Ranpo98/Safe_Crib_with_Auto_Detection/CAD/1.JPG

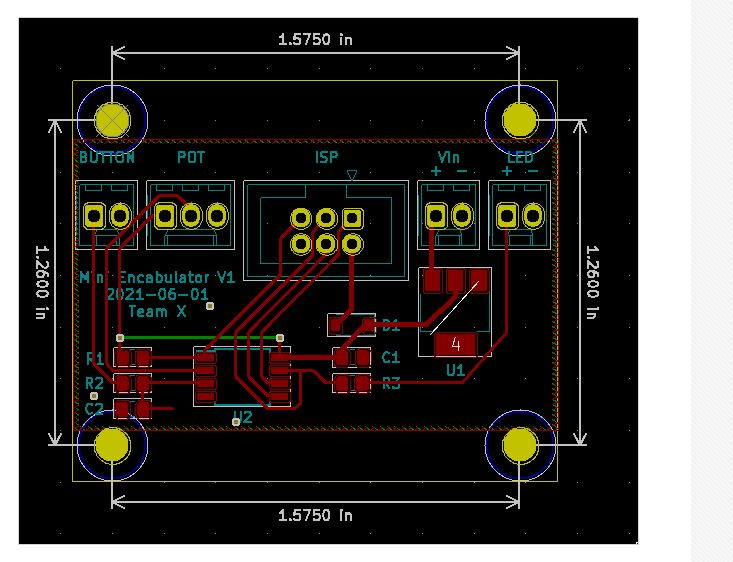
CAD/1.JPG
