Ranpo98/Safe_Crib_with_Auto_Detection/CAD/2.JPG

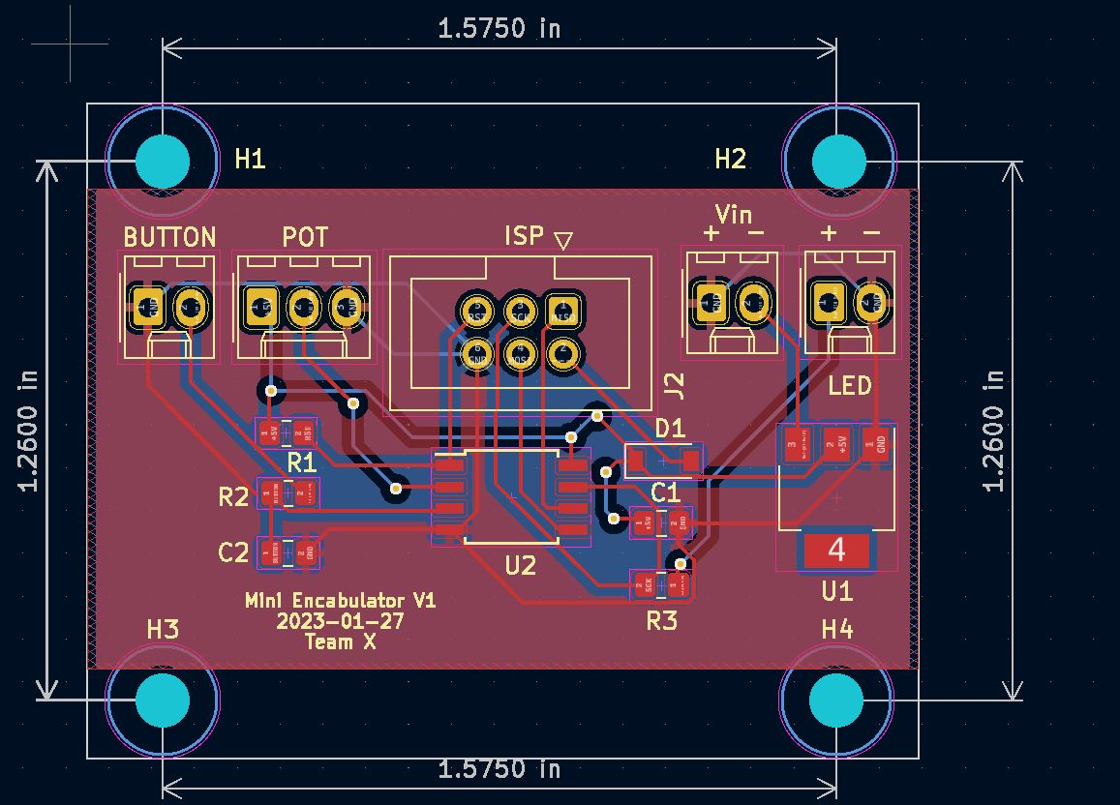
CAD/2.JPG
