Ranpo98/Safe_Crib_with_Auto_Detection/CAD/[fengz3]_miniencabulator/4.JPG

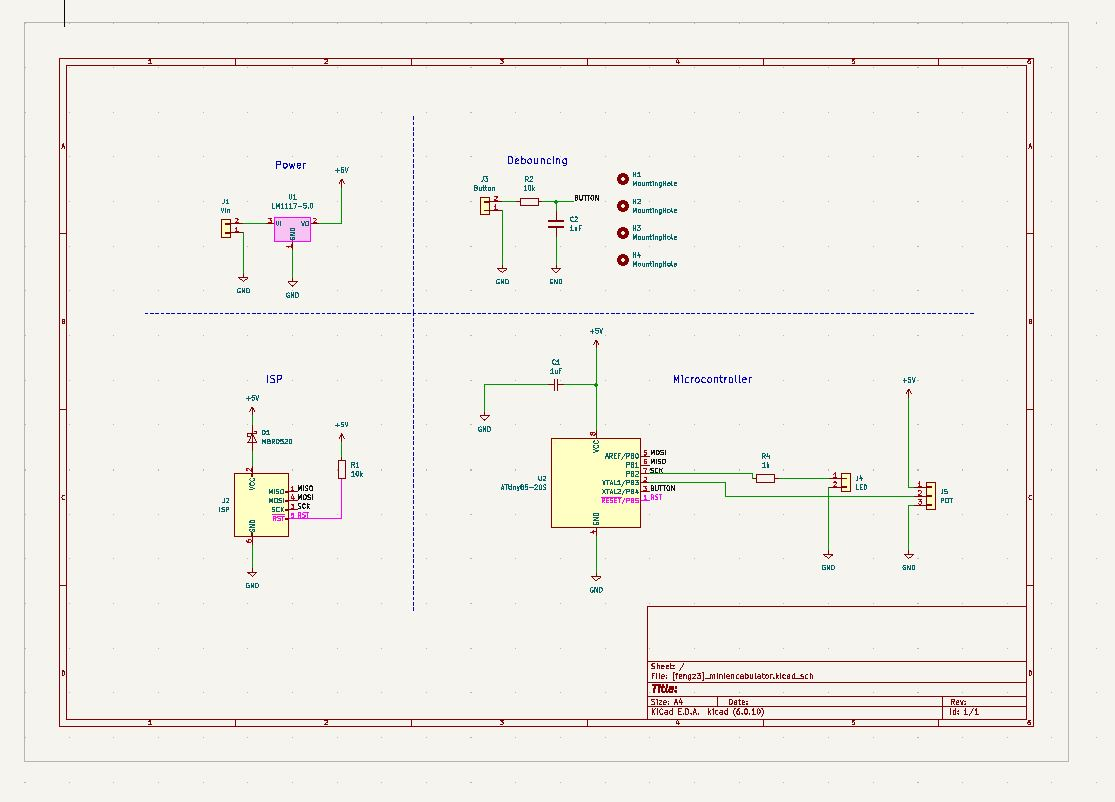
CAD/[fengz3]_miniencabulator/4.JPG
