Ranpo98/Safe_Crib_with_Auto_Detection/Feng's Notebooks/crib model.png

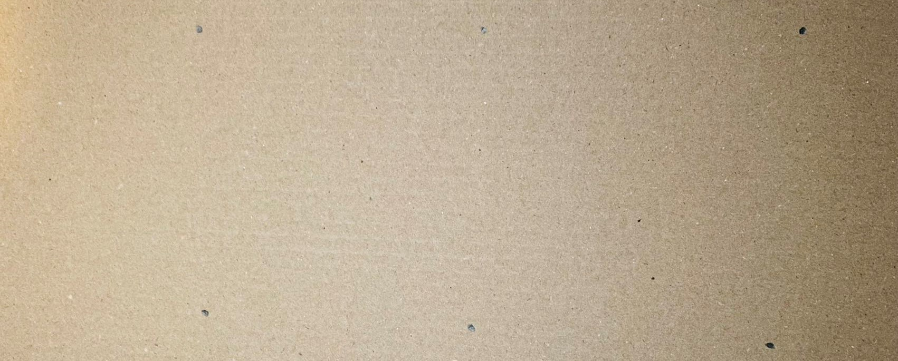
Feng's Notebooks/crib model.png
