Ranpo98/Safe_Crib_with_Auto_Detection/Feng's Notebooks/crosstalk 2.PNG

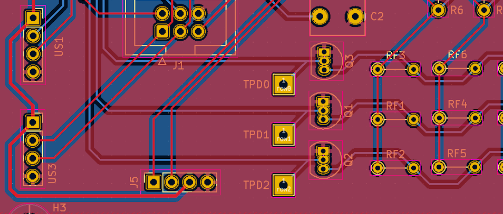
Feng's Notebooks/crosstalk 2.PNG
