Ranpo98/Safe_Crib_with_Auto_Detection/Feng's Notebooks/N3.jpg

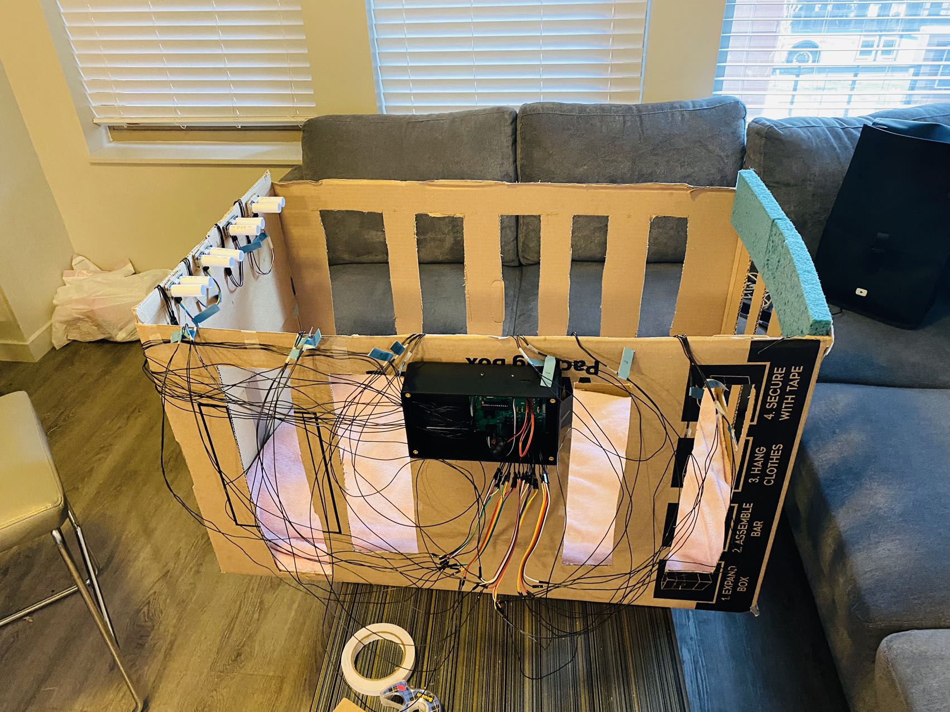
Feng's Notebooks/N3.jpg
