Ranpo98/Safe_Crib_with_Auto_Detection/Feng's Notebooks/N4.jpg

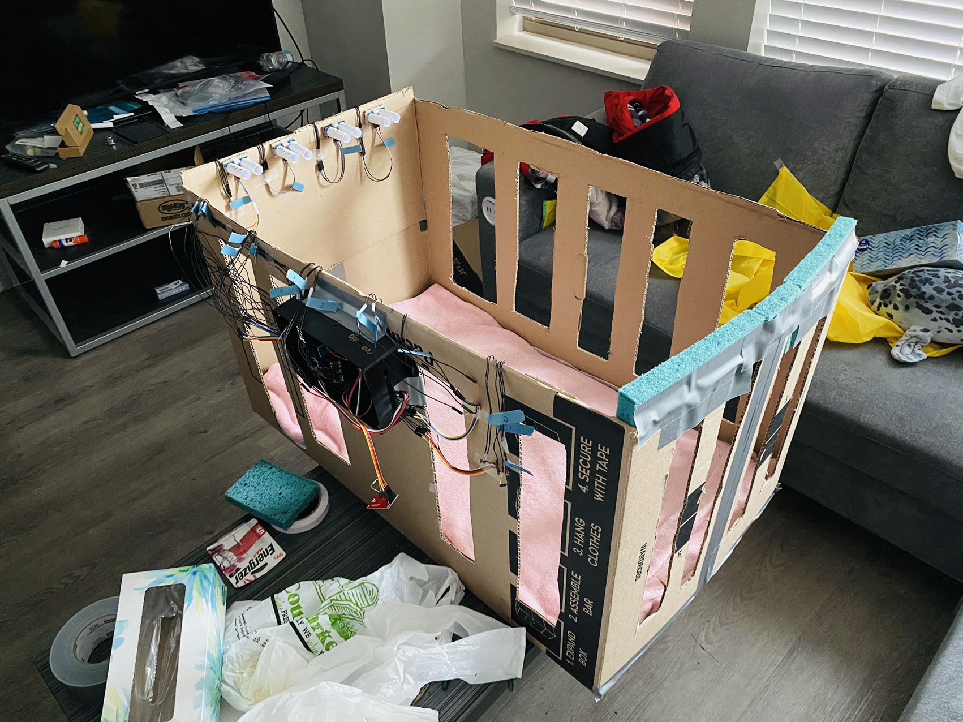
Feng's Notebooks/N4.jpg
