Ranpo98/Safe_Crib_with_Auto_Detection/Feng's Notebooks/Table_Sound.PNG

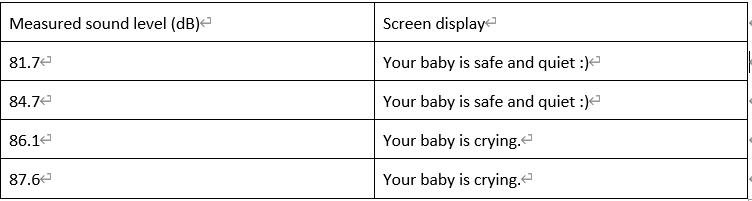
Feng's Notebooks/Table_Sound.PNG
