Ranpo98/Safe_Crib_with_Auto_Detection/Images/image7.png

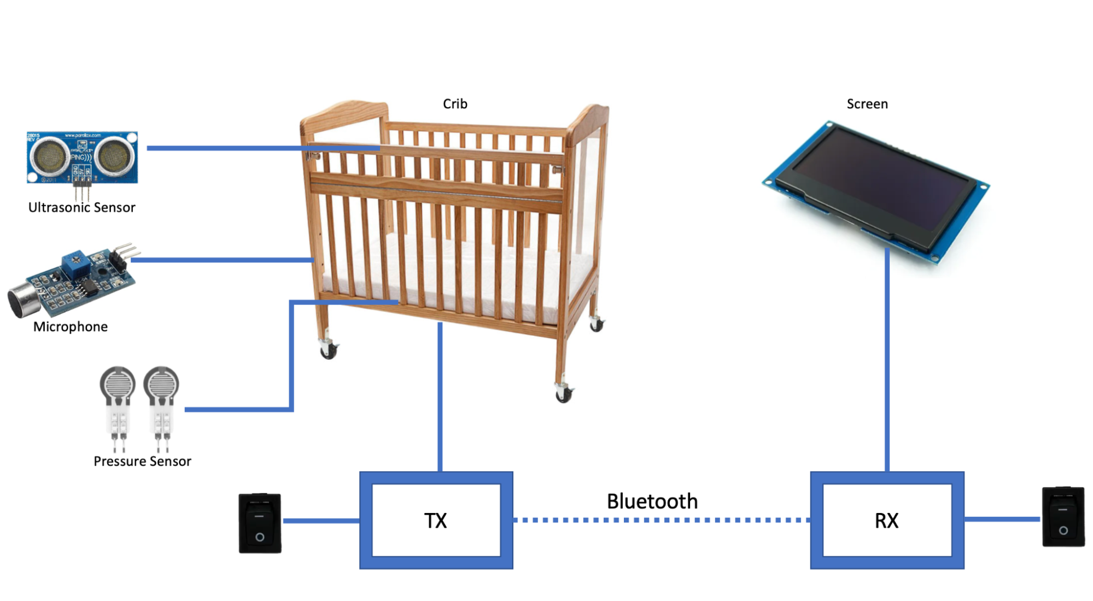
Images/image7.png
