Ranpo98/Safe_Crib_with_Auto_Detection/Images/image8.png

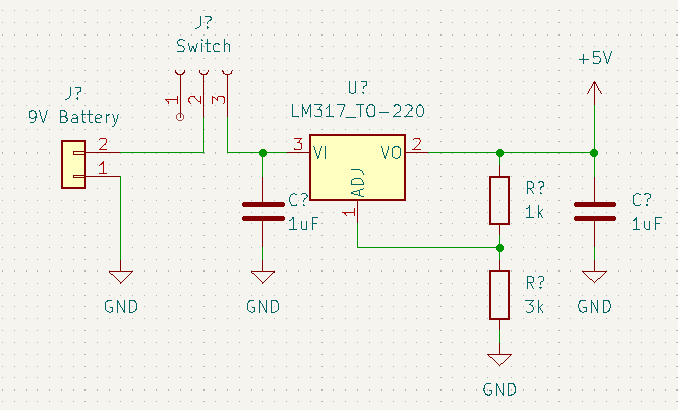
Images/image8.png
