Ranpo98/Safe_Crib_with_Auto_Detection/Images/image9.png

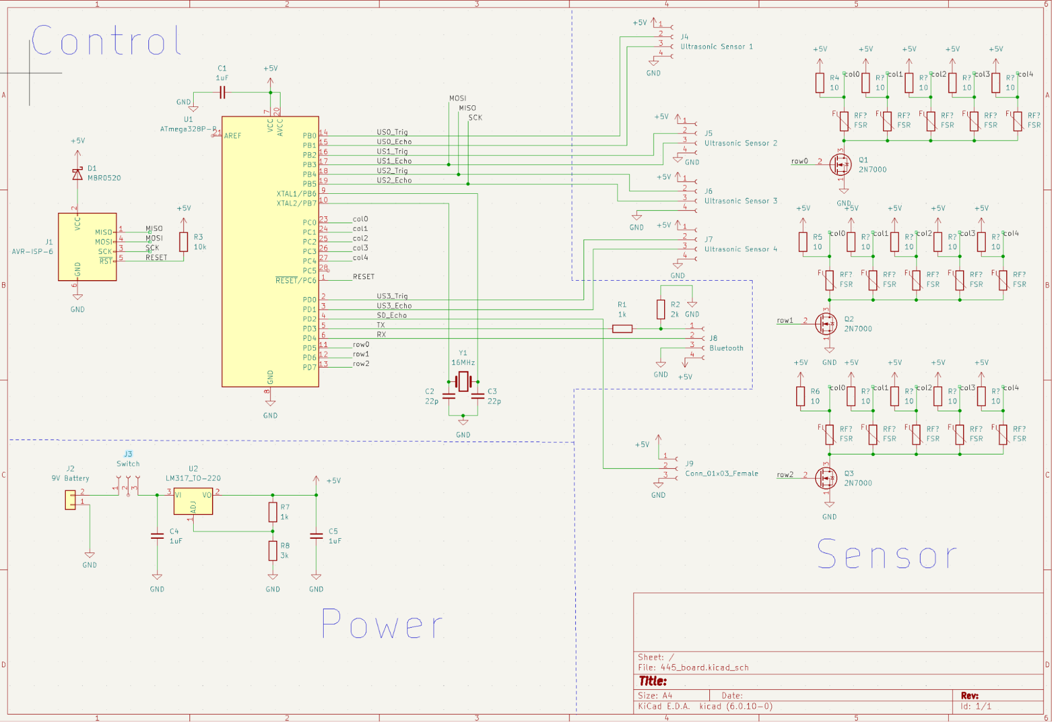
Images/image9.png
