Ranpo98/Safe_Crib_with_Auto_Detection/Images/image10.png

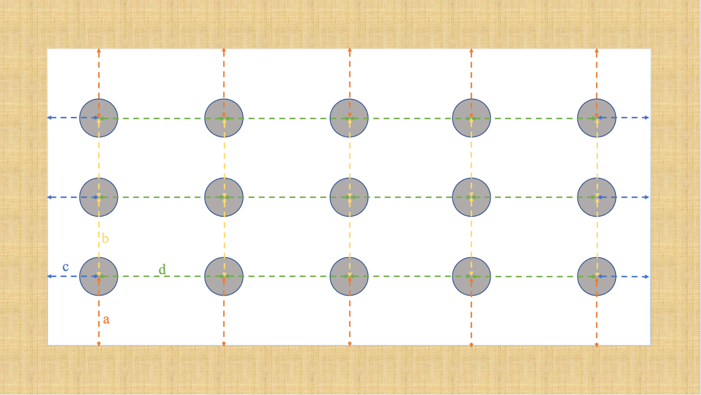
Images/image10.png
