Ranpo98/Safe_Crib_with_Auto_Detection/Images/image13.png

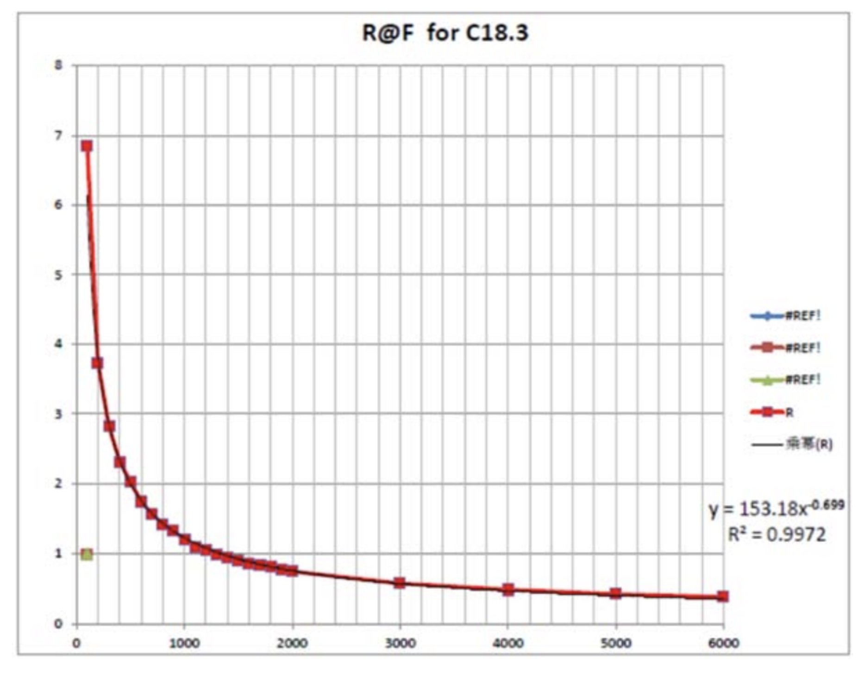
Images/image13.png
