Ranpo98/Safe_Crib_with_Auto_Detection/Images/image14.png

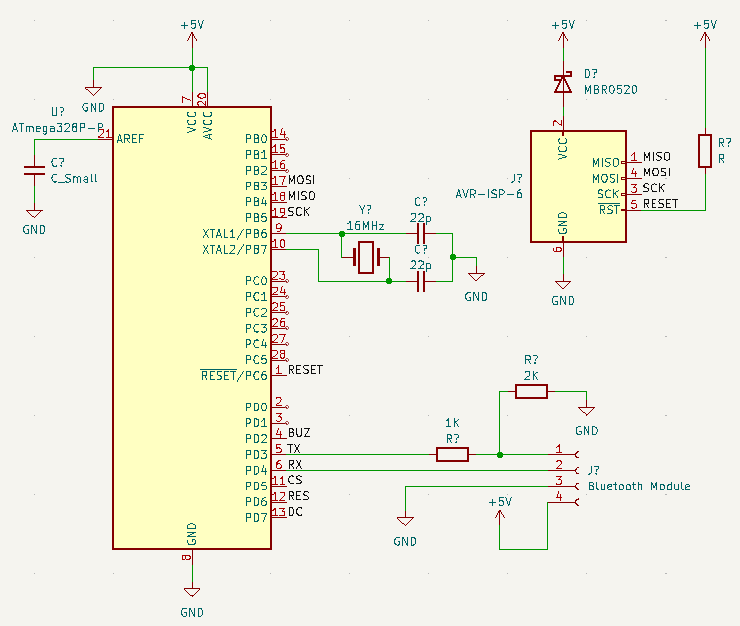
Images/image14.png
