Ranpo98/Safe_Crib_with_Auto_Detection/Images/image15.png

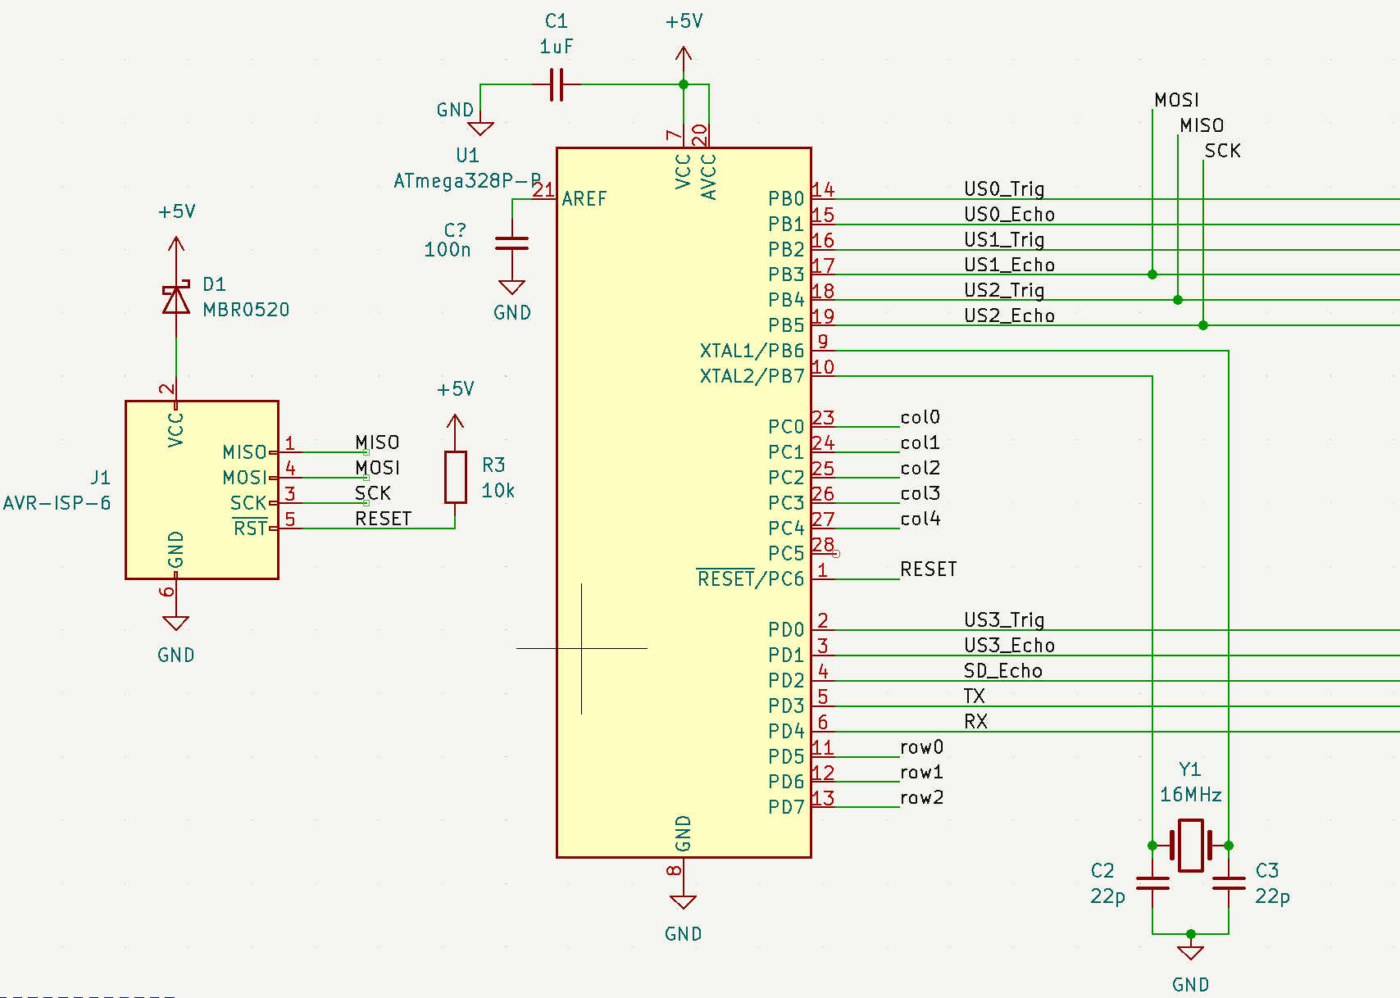
Images/image15.png
