Ranpo98/Safe_Crib_with_Auto_Detection/Images/image16.png

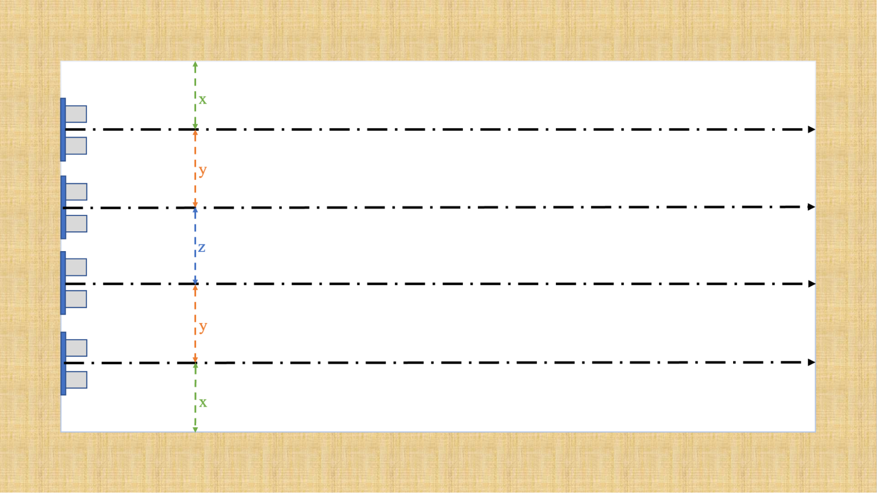
Images/image16.png
