Ranpo98/Safe_Crib_with_Auto_Detection/Images/image17.png

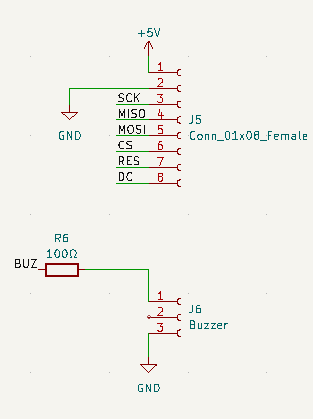
Images/image17.png
