Ranpo98/Safe_Crib_with_Auto_Detection/Images/image18.png

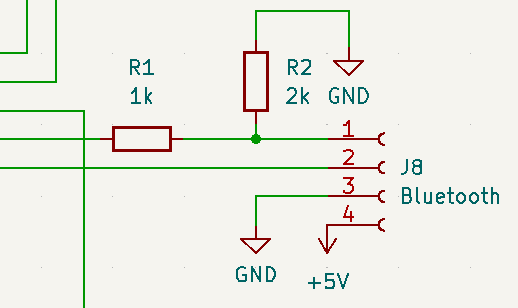
Images/image18.png
