Ranpo98/Safe_Crib_with_Auto_Detection/Images/image20.png

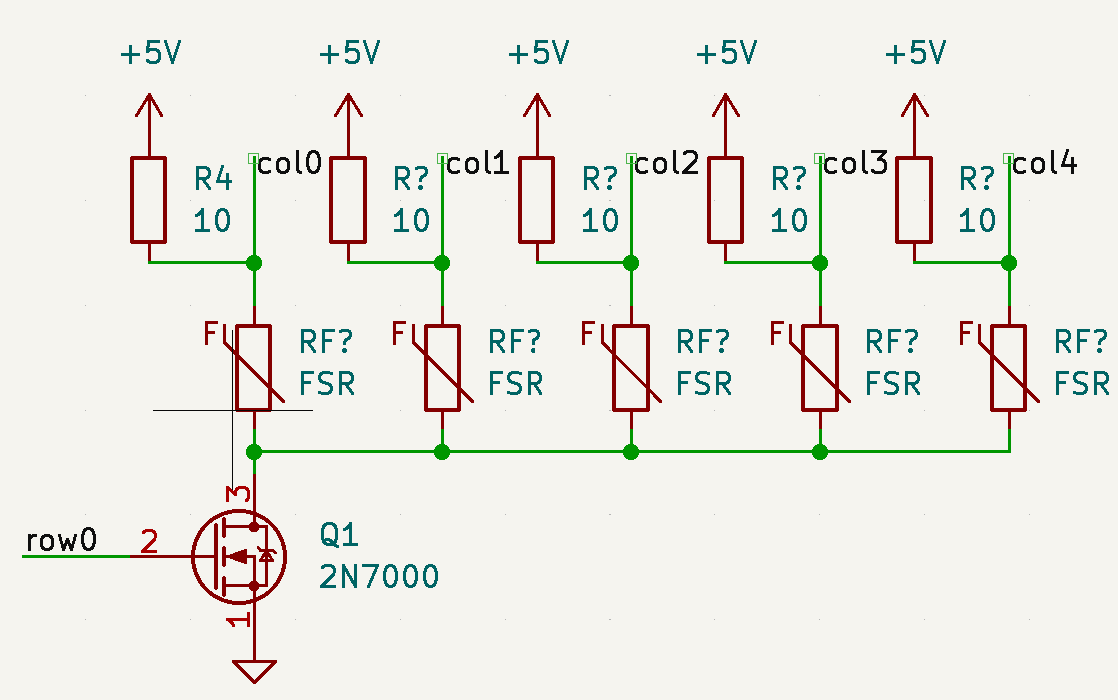
Images/image20.png
