Ranpo98/Safe_Crib_with_Auto_Detection/Images/Monitor.jpg

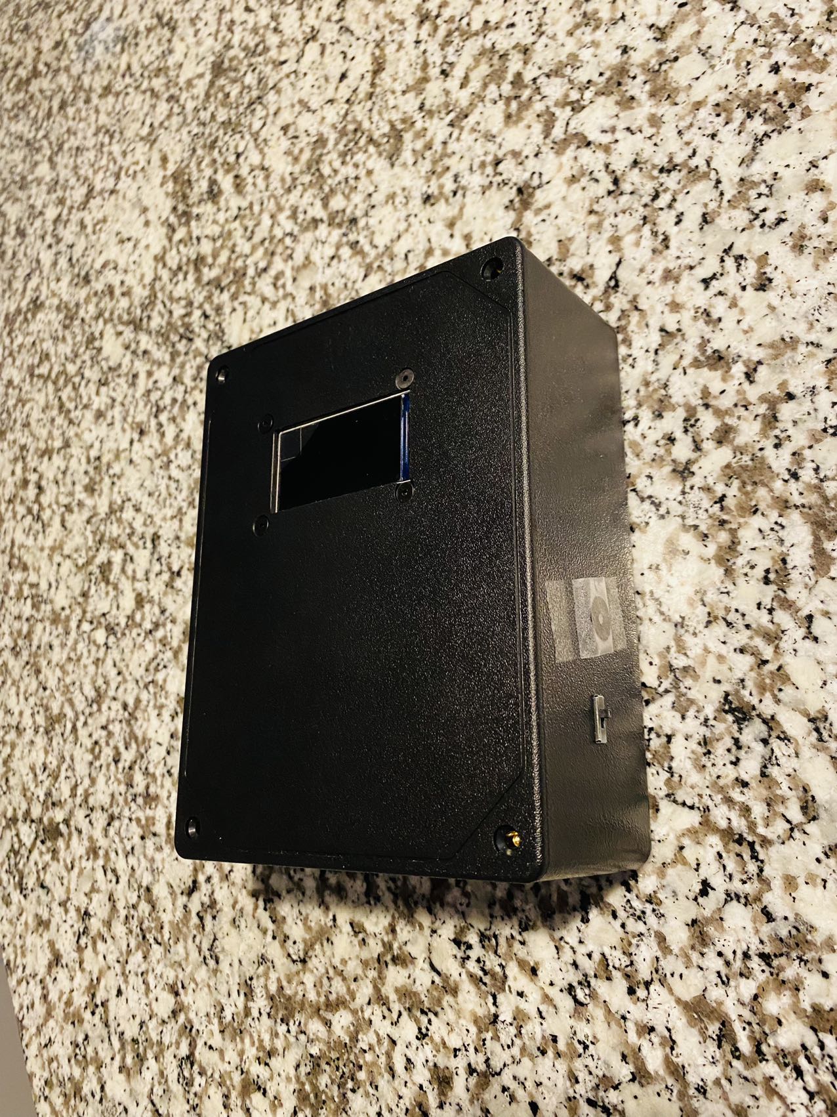
Images/Monitor.jpg
