Ranpo98/Safe_Crib_with_Auto_Detection/Images/Sensors_plot2.png

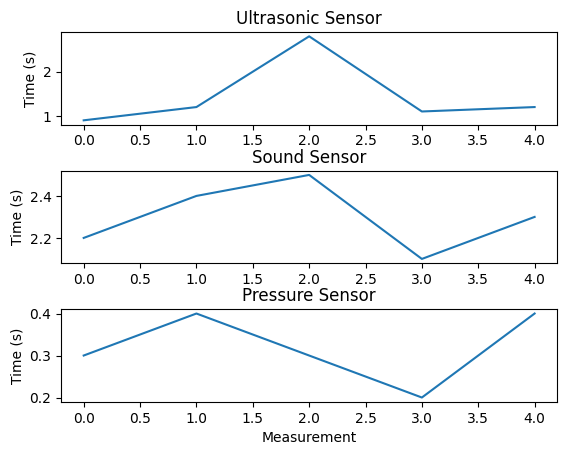
Images/Sensors_plot2.png
