Ranpo98/Safe_Crib_with_Auto_Detection/Images/Sensors_plot3.png

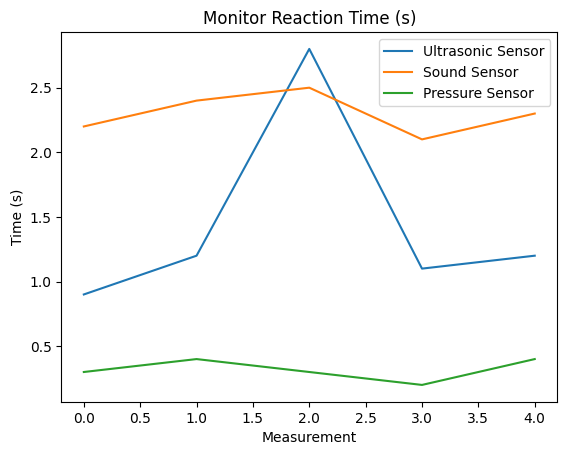
Images/Sensors_plot3.png
