Ranpo98/Safe_Crib_with_Auto_Detection/Individual Progress Report/PCB_pressure_sensors.png

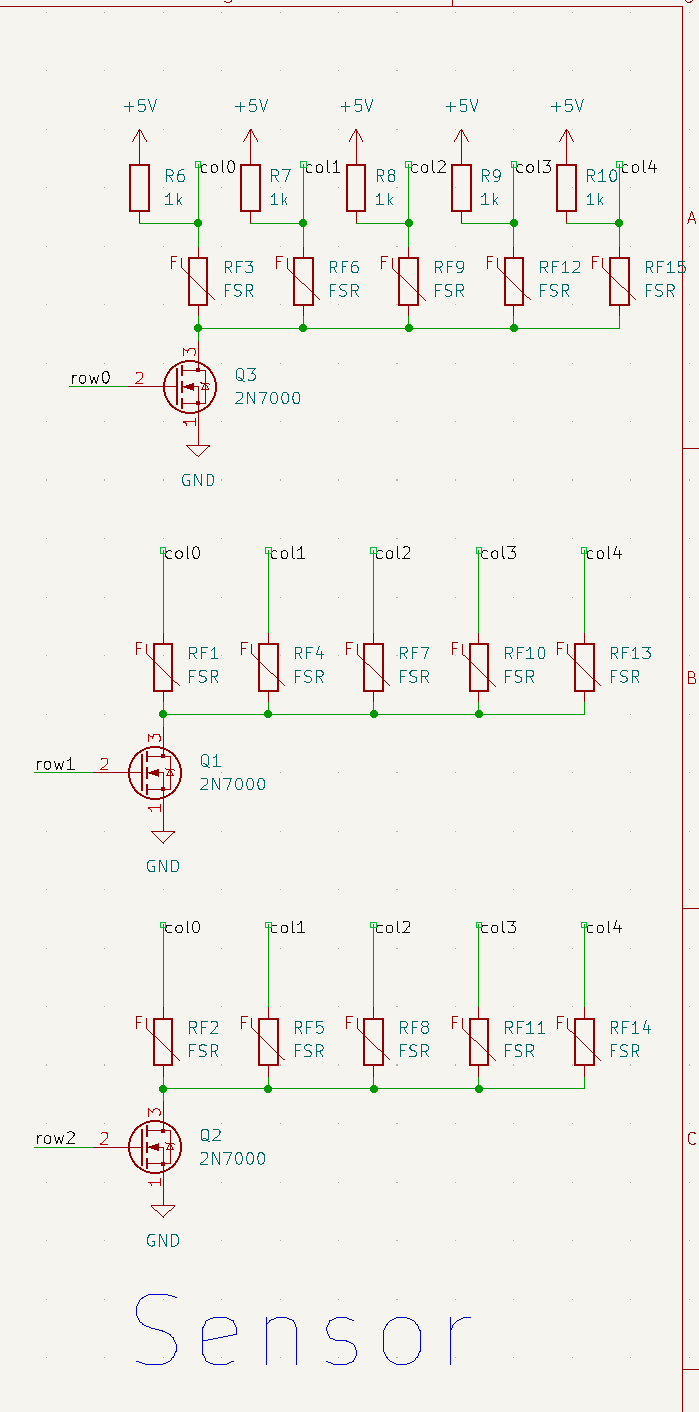
Individual Progress Report/PCB_pressure_sensors.png
