Ranpo98/Safe_Crib_with_Auto_Detection/Individual Progress Report/sound sensor code 1.JPG

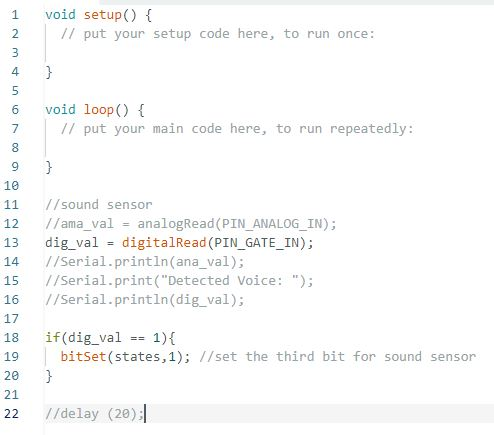
Individual Progress Report/sound sensor code 1.JPG
