Ranpo98/Safe_Crib_with_Auto_Detection/Individual Progress Report/ultrasonic sensor code 2.JPG

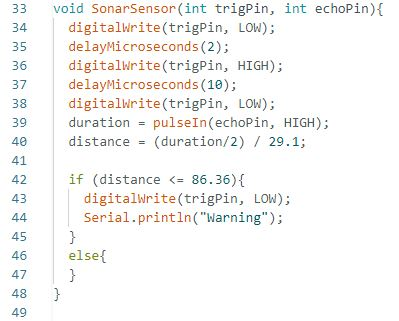
Individual Progress Report/ultrasonic sensor code 2.JPG
