Ranpo98/Safe_Crib_with_Auto_Detection/RV/Crib power.JPG

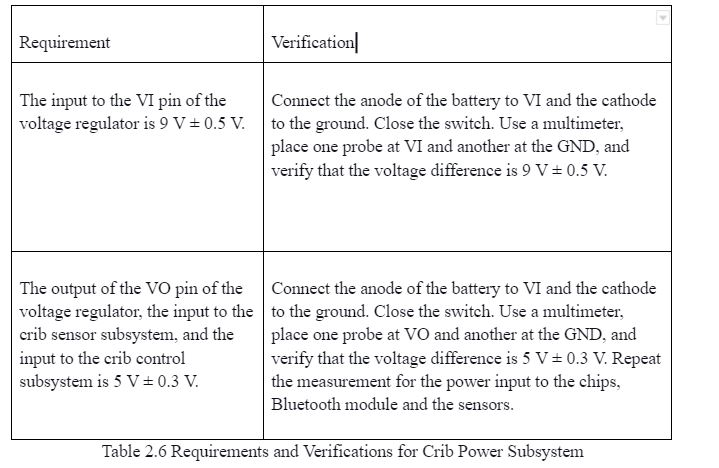
RV/Crib power.JPG
