Ranpo98/Safe_Crib_with_Auto_Detection/RV/UI.JPG

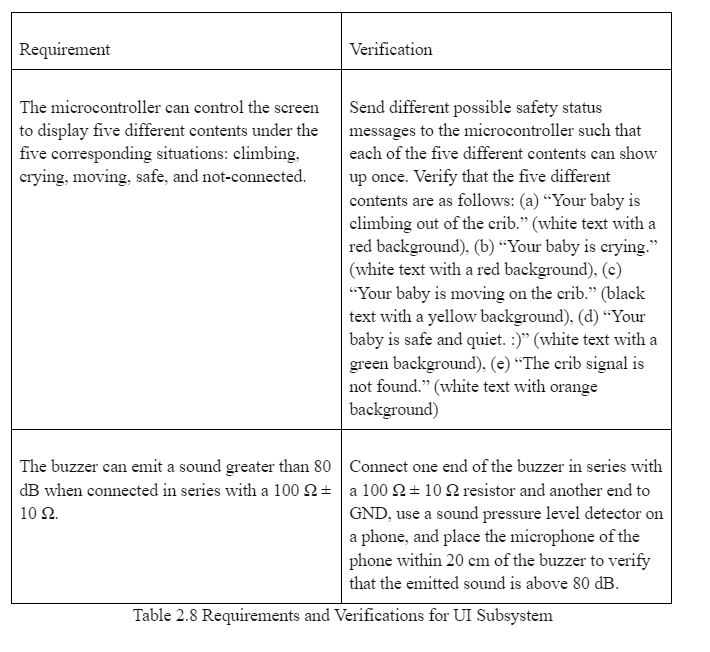
RV/UI.JPG
