Ranpo98/Safe_Crib_with_Auto_Detection/Videos/1.jpg

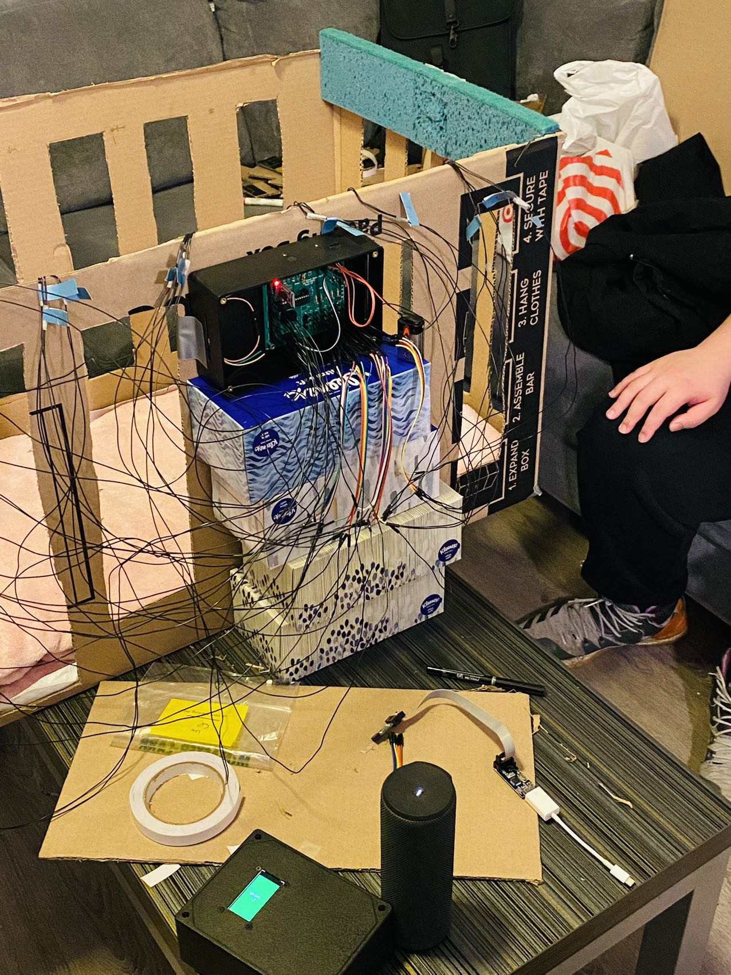
Videos/1.jpg
